PatternAgents/CPM_Pmod/CPM_Pmod/eagleUp/eagleUp_CPM_Pmod_bottom.png

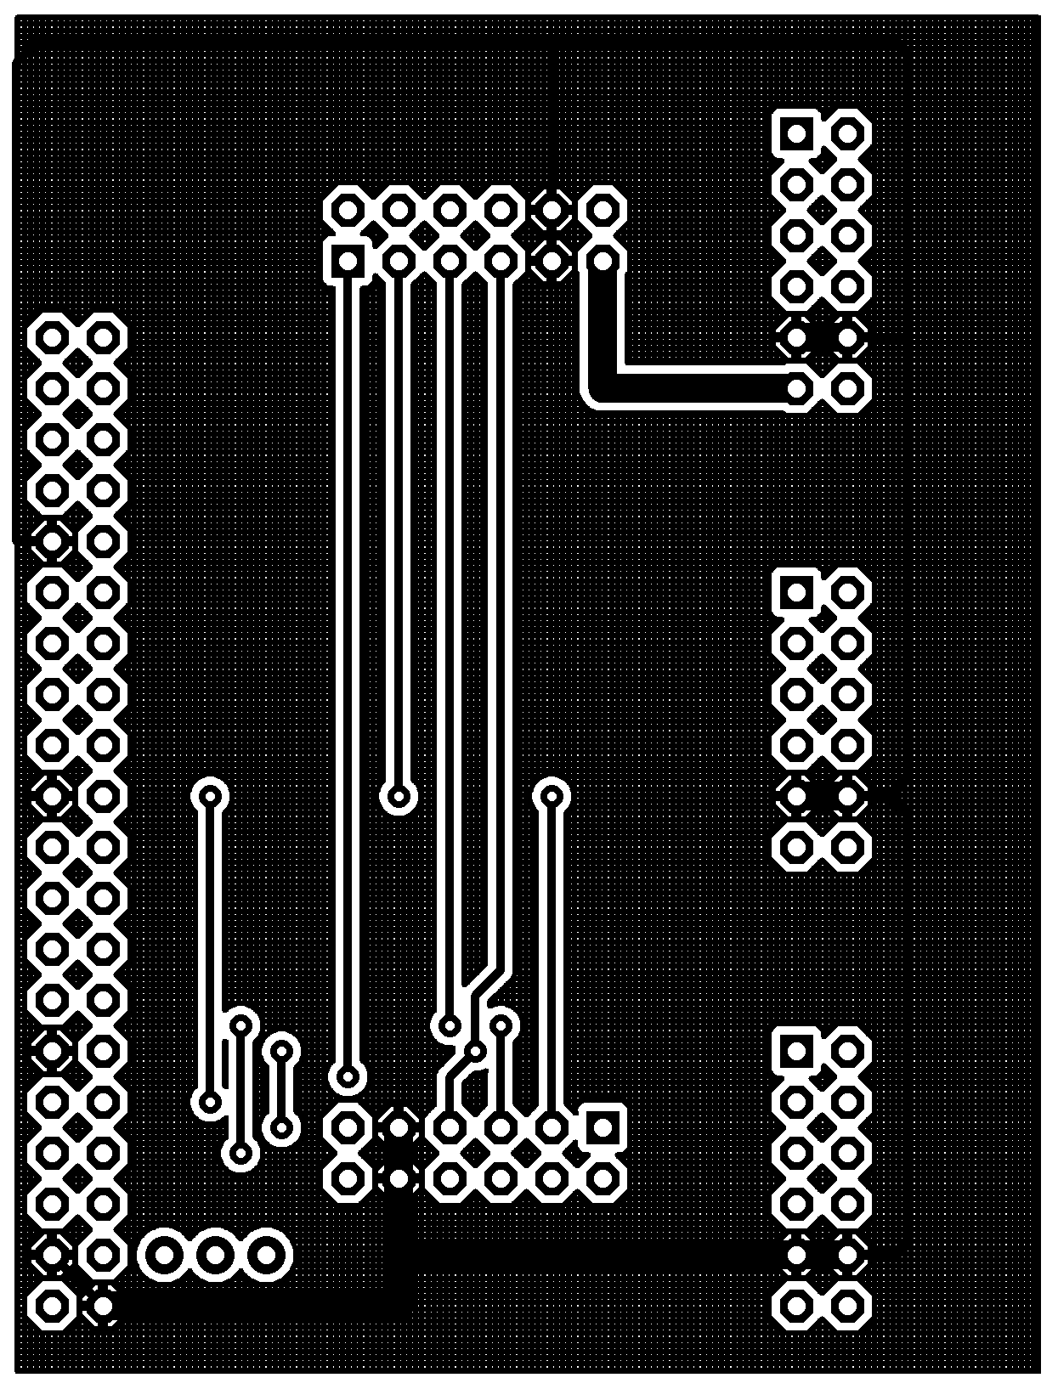
CPM_Pmod/eagleUp/eagleUp_CPM_Pmod_bottom.png
