PatternAgents/CPM_Pmod/CPM_Pmod/eagleUp/eagleUp_CPM_Pmod_imagesize.png

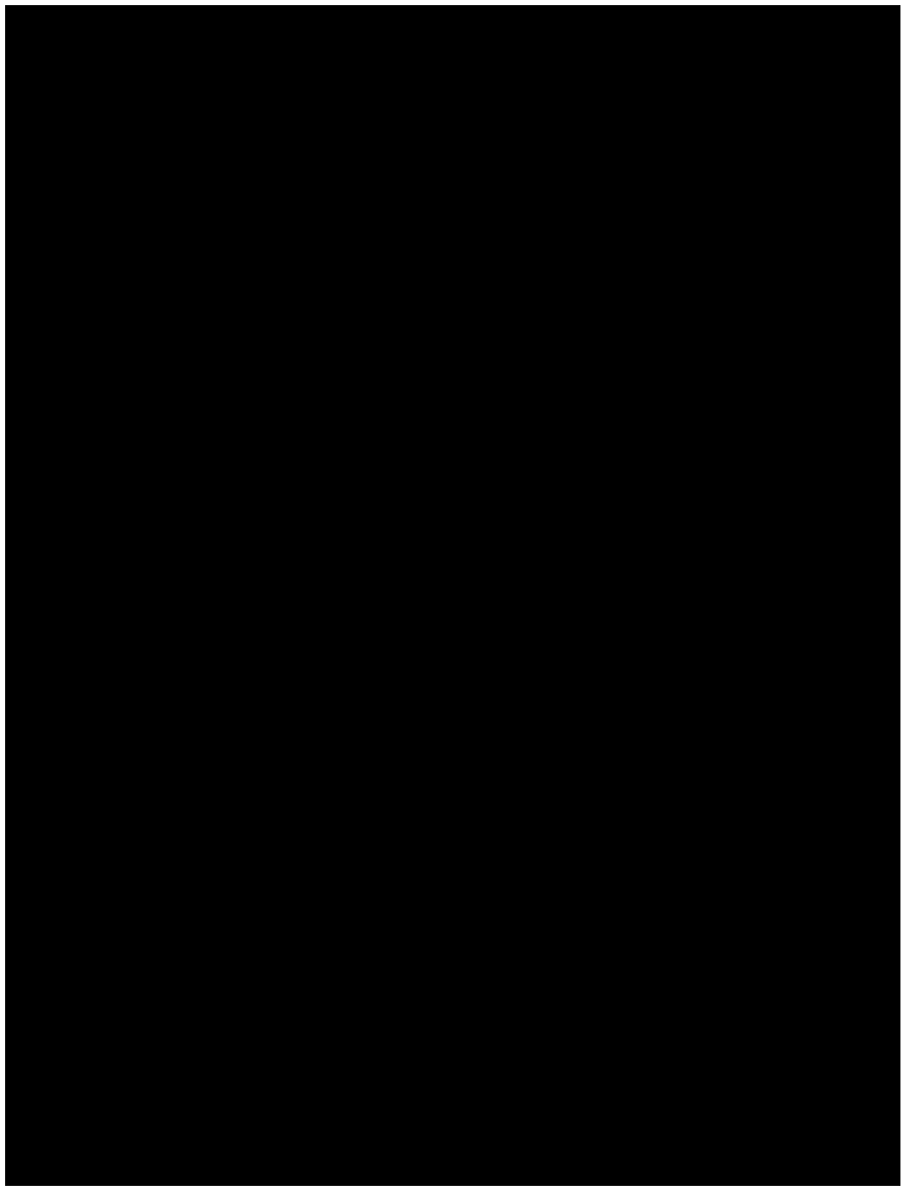
CPM_Pmod/eagleUp/eagleUp_CPM_Pmod_imagesize.png
