PatternAgents/CPM_Pmod/CPM_Pmod/eagleUp/eagleUp_CPM_Pmod_top.png

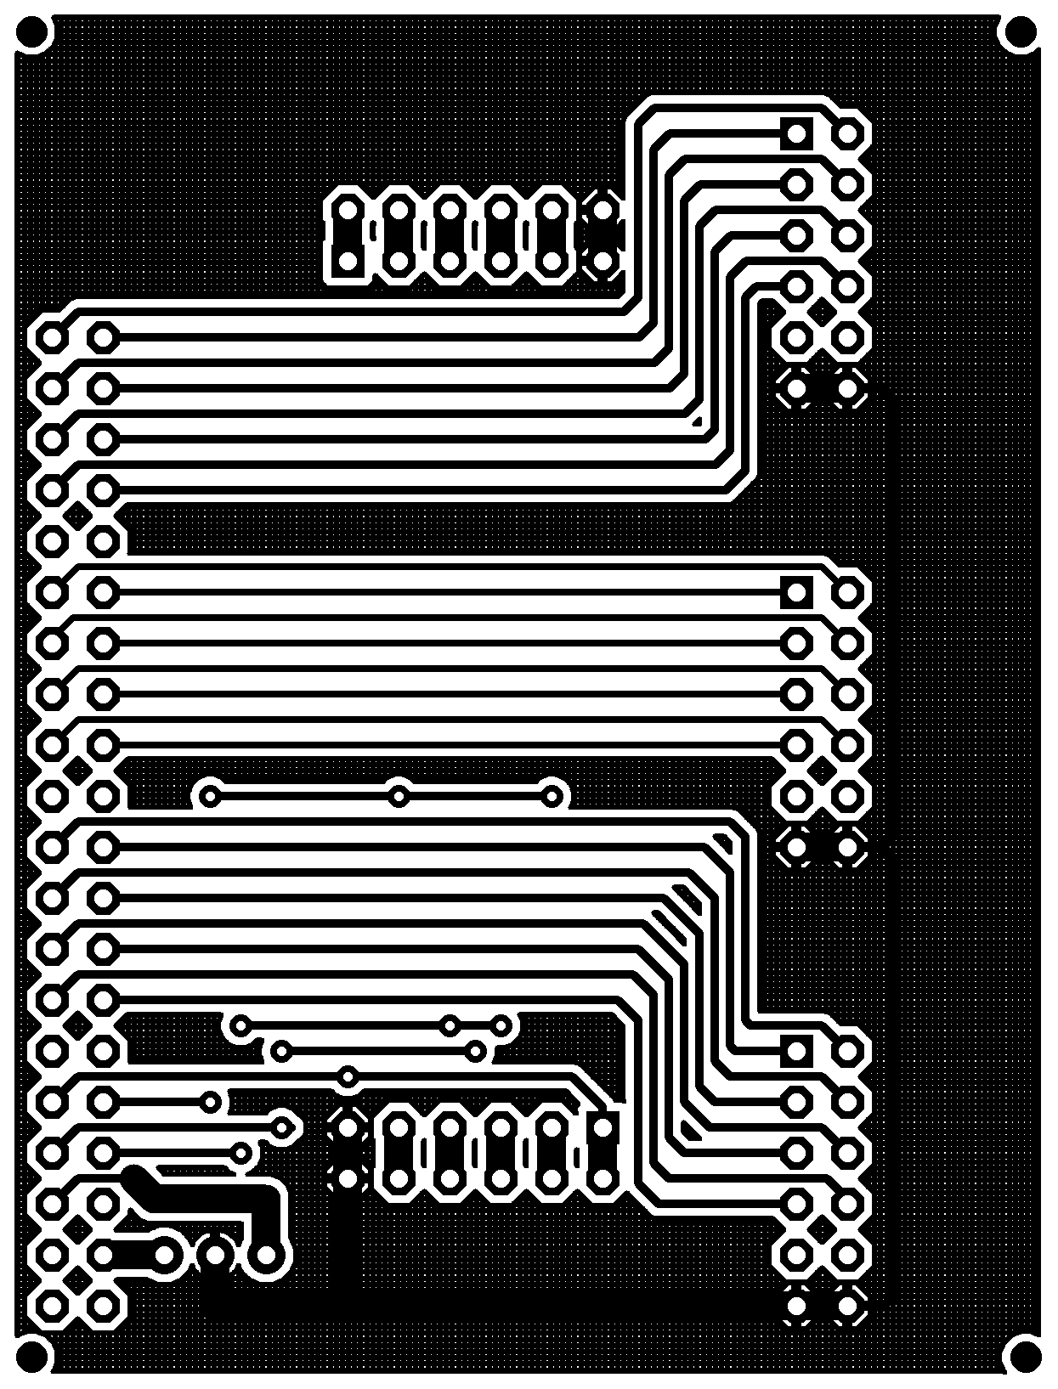
CPM_Pmod/eagleUp/eagleUp_CPM_Pmod_top.png
